wlyoung/8x8-Shelter/dxf files/half inch/Interior wall and purlin cut 2.dxf

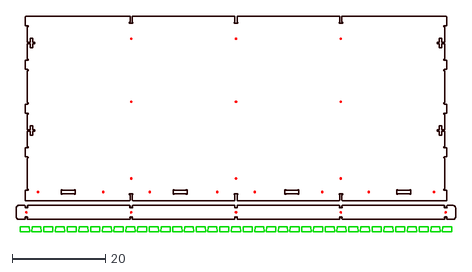
[picture p15: CAD file, 2017-06-12]
dxf files/half inch/Interior wall and purlin cut 2.dxf
94.2 x 46.1
